matthiasjordan/openpaddle/paddle/paddle.scad

include<paddle-large.scad>
