matthiasjordan/openpaddle/pico/paddle.scad

include<../paddle/paddle-large.scad>
