matthiasjordan/openpaddle/plain/paddle.scad

include<../paddle/paddle-large.scad>
